Agrabski/exacto/firmware/src/settings.rs

mod rendering;
mod sub_menus;
mod ui;

use crate::{
    buttons::ButtonEvent,
    settings::{
        sub_menus::{about_page::{AboutPage, ABOUT_PAGE}, main_menu::{MainMenuState, MainMenuType, MAIN_MENU}, sight_menu::{SightMenu, SIGHT_MENU}},
        ui::{settings_page::SettingsPageState, ClickResult, SubMenuPointer, SubMenuPointerImpl},
    },
    sight::Sight,
};
use core::fmt::Debug;
use embedded_graphics::{
    pixelcolor::Rgb565,
    prelude::DrawTarget,
};

pub struct SettingsState {
    current_menu: Option<SettingsMenu>,
    states: SubMenuStates,
}

#[derive(Debug, Clone, Copy)]
enum RotorInput {
    Up,
    Down,
}

#[derive(Debug, Clone, Copy)]
enum SettingsMenu {
    MainMenu,
    Sight,
    Settings,
    About,
}


struct SubMenuStates {
    main_menu: SubMenuPointerImpl<MainMenuType>,
    sight_settings: SubMenuPointerImpl<SightMenu>, // Placeholder for other submenus
    about: SubMenuPointerImpl<AboutPage>, // Placeholder for the about submenu
}

impl SubMenuStates {
    pub fn new() -> Self {
        Self {
            main_menu: SubMenuPointerImpl {
                submenu: &MAIN_MENU,
                state: MainMenuState { selected_index: 0 },
            },
            sight_settings: SubMenuPointerImpl {
                submenu: &SIGHT_MENU,
                state: SettingsPageState::new(),
            },
            about: SubMenuPointerImpl {
                submenu: &ABOUT_PAGE,
                state: SettingsPageState::new(),
            },
        }
    }

    pub fn get_menu<'a>(&'a mut self, menu: SettingsMenu) -> Option<&'a mut dyn SubMenuPointer> {
        match menu {
            SettingsMenu::MainMenu => Some(&mut self.main_menu),
            SettingsMenu::Sight => Some(&mut self.sight_settings),
            SettingsMenu::About => Some(&mut self .about),
            _ => None,
        }
    }

    pub fn get_menu_const<'a>(&'a self, menu: SettingsMenu) -> Option<&'a dyn SubMenuPointer> {
        match menu {
            SettingsMenu::MainMenu => Some(&self.main_menu),
            SettingsMenu::Sight => Some(&self.sight_settings),
            SettingsMenu::About => Some(&self .about),
            _ => None,
        }
    }
}

impl SettingsState {
    pub fn new() -> Self {
        Self {
            current_menu: None,
            states: SubMenuStates::new(),
        }
    }

    pub fn is_open(&self) -> bool {
        self.current_menu.is_some()
    }

    pub fn update(&mut self, sight: &mut Sight, event: Option<ButtonEvent>) -> bool {
        match event {
            Some(ButtonEvent::Select) => self.handle_press(sight),
            Some(ButtonEvent::Up) => self.handle_rotation(sight, RotorInput::Up),
            Some(ButtonEvent::Down) => self.handle_rotation(sight, RotorInput::Down),
            None => false,
        }
    }

    pub fn draw<DI>(&self, display: &mut DI, sight: &Sight)
    where
        DI: DrawTarget<Color = Rgb565, Error: Debug>,
    {
        if let Some(menu) = &self.current_menu {
            let mut renderer = rendering::DefaultSettingsRenderer { display };
            let sub_menu = self.states.get_menu_const(*menu).unwrap_or_else(|| {
                panic!();
            });
            sub_menu.draw(&mut renderer, sight);
        }
    }

    fn handle_rotation(&mut self, sight: &mut Sight, change: RotorInput) -> bool {
        if let Some(menu) = self.current_menu.as_mut() {
            let sub_menu = self.states.get_menu(menu.clone()).unwrap_or_else(|| {
                panic!();
            });
            sub_menu.handle_input(sight, change);
            true
        } else {
            false
        }
    }

    fn handle_press(&mut self, sight: &mut Sight) -> bool {
        if let Some(menu) = self.current_menu.as_mut() {
            let sub_menu = self.states.get_menu(menu.clone()).unwrap_or_else(|| {
                panic!();
            });
            match sub_menu.handle_click(sight) {
                ClickResult::Navigate(next_menu) => {
                    self.current_menu = Some(next_menu);
                }
                ClickResult::Back => {
                    self.current_menu = None;
                }
                ClickResult::None => {}
            }
        } else {
            self.current_menu = Some(SettingsMenu::MainMenu);
        }
        true
    }
}
